Jacobalicious/Temperature-Sensor-over-Matter-Thread/Real Layout/Topside.jpg

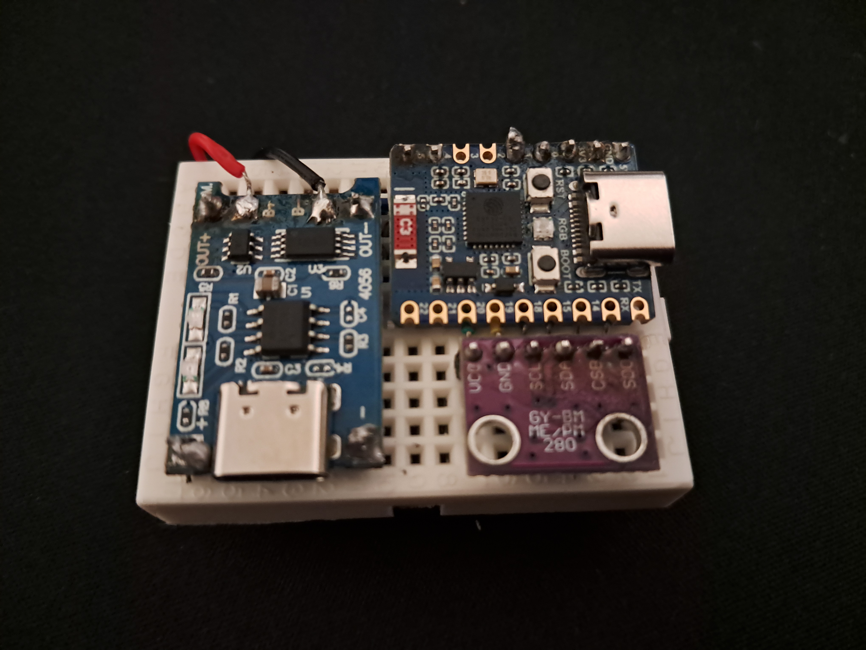
Real Layout/Topside.jpg
